pdropes/Esp32---Pac-man/esp32_Pacman/PacmanTiles.h

/******************************************************************************/
/*                                                                            */
/*  PACMAN GAME FOR ARDUINO DUE                                               */
/*                                                                            */
/******************************************************************************/
/*  Copyright (c) 2014  Dr. NCX (mirracle.mxx@gmail.com)                      */
/*                                                                            */
/* THE SOFTWARE IS PROVIDED "AS IS" AND THE AUTHOR DISCLAIMS ALL              */
/* WARRANTIES WITH REGARD TO THIS SOFTWARE INCLUDING ALL IMPLIED              */
/* WARRANTIES OF MERCHANTABILITY AND FITNESS. IN NO EVENT SHALL THE AUTHOR    */
/* BE LIABLE FOR ANY SPECIAL, DIRECT, INDIRECT, OR CONSEQUENTIAL DAMAGES      */
/* OR ANY DAMAGES WHATSOEVER RESULTING FROM LOSS OF USE, DATA OR PROFITS,     */
/* WHETHER IN AN ACTION OF CONTRACT, NEGLIGENCE OR OTHER TORTIOUS ACTION,     */
/* ARISING OUT OF OR IN CONNECTION WITH THE USE OR PERFORMANCE OF THIS        */
/* SOFTWARE.                                                                  */
/*                                                                            */
/*  MIT license, all text above must be included in any redistribution.       */


#ifndef byte
typedef unsigned char byte;
typedef unsigned short ushort;
typedef unsigned long ulong;
#endif

#ifndef uchar
typedef unsigned char uchar;
#endif

#define PROGMEM 
typedef unsigned char uint8_t;
typedef unsigned short uint16_t;
//typedef unsigned long uint32_t;
#define pgm_read_byte(_x) (*(_x))
#define pgm_read_word(_x) (*(_x))


#ifndef _max
#define _max(_a,_b) (((_a) > (_b)) ? (_a) : (_b))
#define _min(_a,_b) (((_a) < (_b)) ? (_a) : (_b))
#endif

#define ASSERT(_x) if (!(_x)) assertFailed(NULL,__LINE__);

// Playfield (36 tiles)
const byte playTiles[] = {
0x00,0x00,0x00,0x00,0x00,0x00,0x00,0x00,   // 0
0x0F,0x30,0x40,0x47,0x88,0x90,0x90,0x90,   // 1
0xFF,0x00,0x00,0xFF,0x00,0x00,0x00,0x00,   // 2
0xFF,0x00,0x00,0xE0,0x10,0x08,0x08,0x08,   // 3
0xFF,0x00,0x00,0x07,0x08,0x10,0x10,0x10,   // 4
0xF0,0x0C,0x02,0xE2,0x11,0x09,0x09,0x09,   // 5
0x90,0x90,0x90,0x90,0x90,0x90,0x90,0x90,   // 6
0x00,0x00,0x00,0x18,0x18,0x00,0x00,0x00,   // 7 - Dot
0x08,0x08,0x08,0x08,0x08,0x08,0x08,0x08,   // 8
0x10,0x10,0x10,0x10,0x10,0x10,0x10,0x10,   // 9
0x09,0x09,0x09,0x09,0x09,0x09,0x09,0x09,   // 10
0x00,0x00,0x00,0x00,0x03,0x04,0x08,0x08,   // 11
0x00,0x00,0x00,0x00,0xFF,0x00,0x00,0x00,   // 12
0x00,0x00,0x00,0x00,0xC0,0x20,0x10,0x10,   // 13
0x3C,0x7E,0xFF,0xFF,0xFF,0xFF,0x7E,0x3C,   // 14 - Pill
0x08,0x08,0x04,0x03,0x00,0x00,0x00,0x00,   // 15
0x00,0x00,0x00,0xFF,0x00,0x00,0x00,0x00,   // 16
0x10,0x10,0x20,0xC0,0x00,0x00,0x00,0x00,   // 17
0x00,0x00,0x00,0xE0,0x10,0x08,0x08,0x08,   // 18
0x00,0x00,0x00,0x07,0x08,0x10,0x10,0x10,   // 19
0x90,0x90,0x90,0x88,0x47,0x40,0x30,0x0F,   // 20
0x00,0x00,0x00,0x00,0xFF,0x00,0x00,0xFF,   // 21
0x10,0x10,0x10,0x08,0x07,0x00,0x00,0x00,   // 22
0x08,0x08,0x08,0x10,0xE0,0x00,0x00,0x00,   // 23
0x09,0x09,0x09,0x11,0xE2,0x02,0x0C,0xF0,   // 24
0x00,0x00,0x00,0x00,0x0F,0x08,0x08,0x09,   // 25
0x00,0x00,0x00,0x00,0xFF,0x01,0x01,0xFF,   // 26
0x00,0x00,0x00,0x00,0x00,0xFF,0xFF,0x00,   // 27
0x00,0x00,0x00,0x00,0xFF,0x80,0x80,0xFF,   // 28
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
  0x00, 0xE0, 0x02, 0x00, 0x00, 0xE0, 0x0A, 0x00, 
  0x00, 0xE0, 0x02, 0x00, 0x00, 0xE0, 0x03, 0x00, 
  0x00, 0xE0, 0x02, 0x00, 0x00, 0xE0, 0x0A, 0x00, 
  0x00, 0xE0, 0x02, 0x00, 0x00, 0x80, 0x00, 0x00, 
  0x00, 0x00, 0x00, 0x00, 0x00, 0x00, 0x00, 0x00, 

};
